Iboy-x/FlyIt-rig-V1/yoke/14-Hubspacing.stl

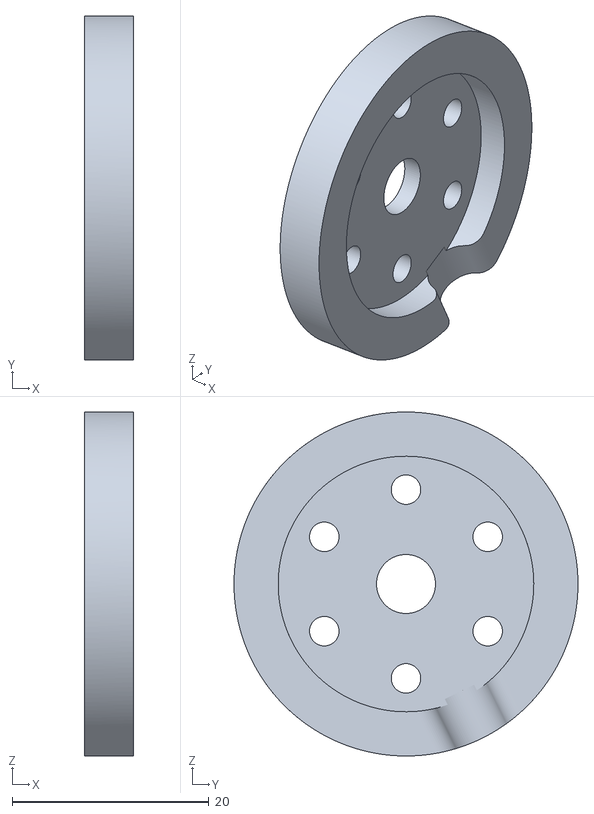
[picture p21: CAD file, 2025-06-05]
yoke/14-Hubspacing.stl
5.00 x 35.0 x 35.0
