Iboy-x/FlyIt-rig-V1/Padel/6-Rod Holder 1.stl

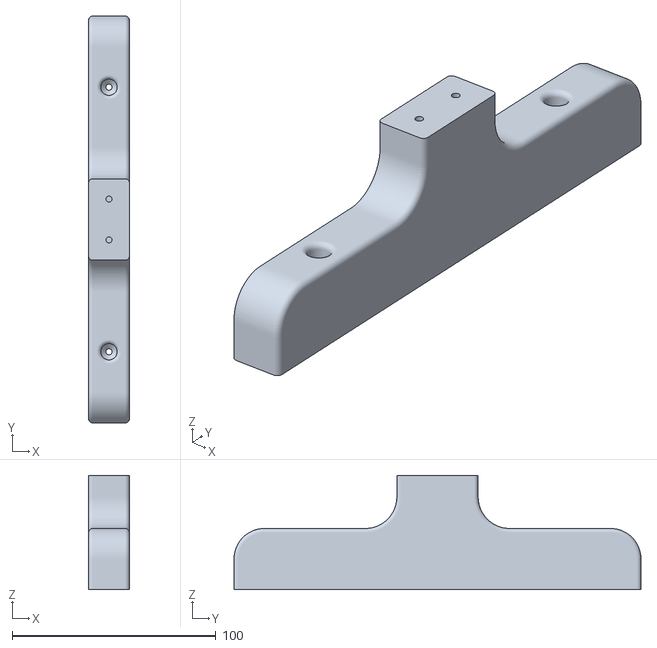
[picture p22: CAD file, 2025-06-15]
Padel/6-Rod Holder 1.stl
20.0 x 200.0 x 56.0
