Iboy-x/FlyIt-rig-V1/yoke/12-LBHupperpart.stl

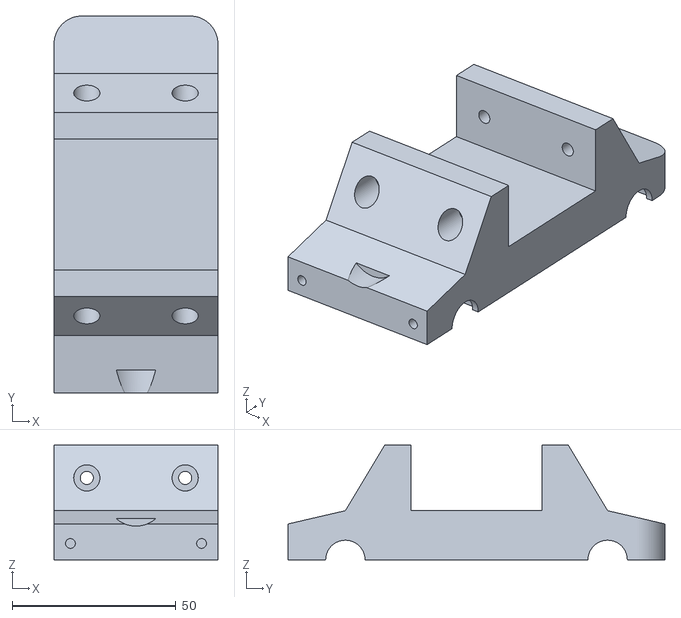
[picture p23: CAD file, 2025-06-05]
yoke/12-LBHupperpart.stl
50.0 x 115.0 x 35.0
