Iboy-x/FlyIt-rig-V1/Padel/1-Padels x2.stl

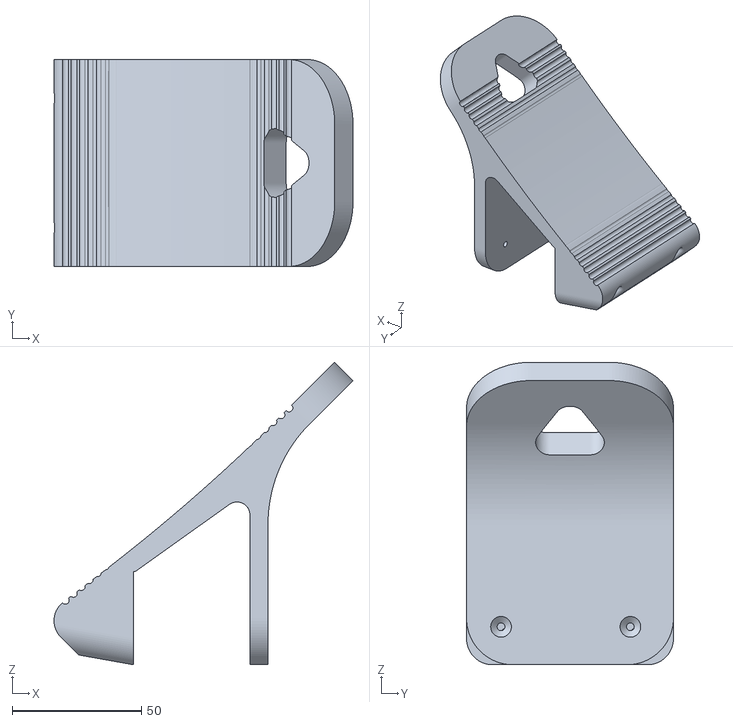
[picture p24: CAD file, 2025-06-15]
Padel/1-Padels x2.stl
115.6 x 80.0 x 116.9
