Iboy-x/FlyIt-rig-V1/Padel/5-Gear-holder.stl

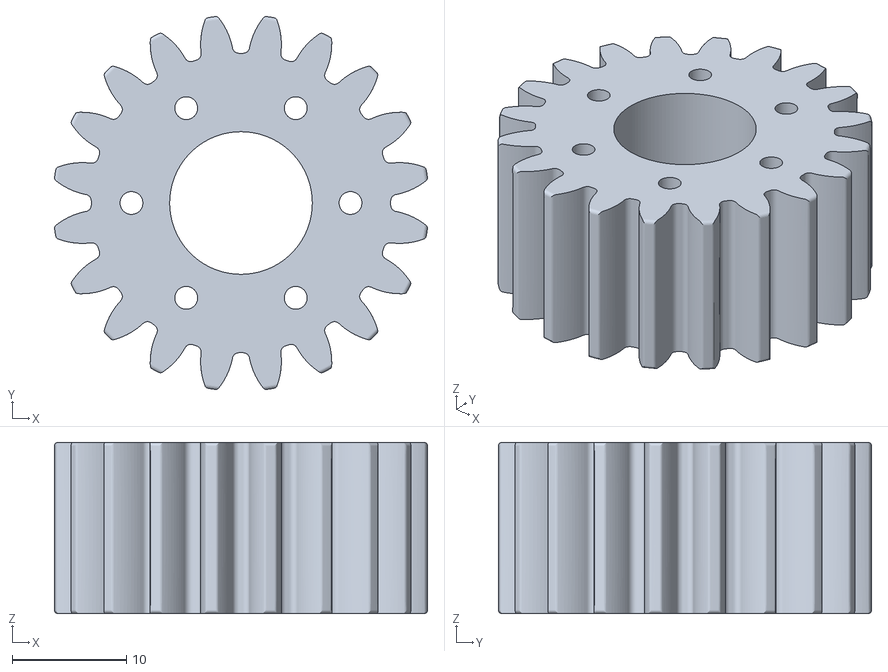
[picture p25: CAD file, 2025-06-15]
Padel/5-Gear-holder.stl
32.7 x 32.7 x 15.0
