Iboy-x/FlyIt-rig-V1/yoke/5-Rodends2.stl

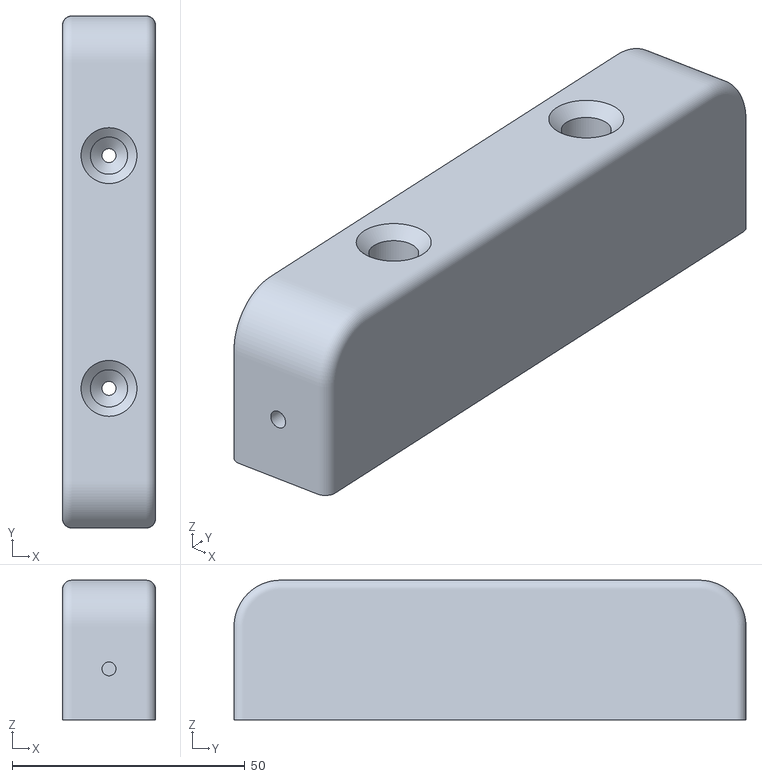
[picture p26: CAD file, 2025-06-05]
yoke/5-Rodends2.stl
20.0 x 110.0 x 30.0
