Iboy-x/FlyIt-rig-V1/Padel/3-BarPadHol.stl

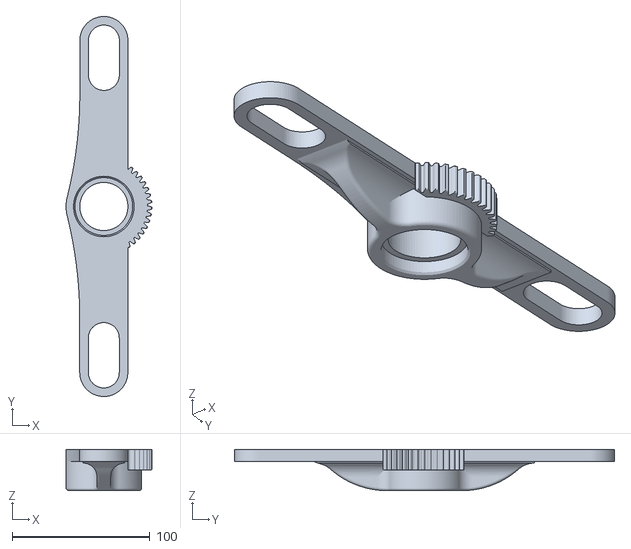
[picture p27: CAD file, 2025-06-15]
Padel/3-BarPadHol.stl
62.5 x 276.3 x 30.0
