Iboy-x/FlyIt-rig-V1/Padel/7- Rod Holder 1.stl

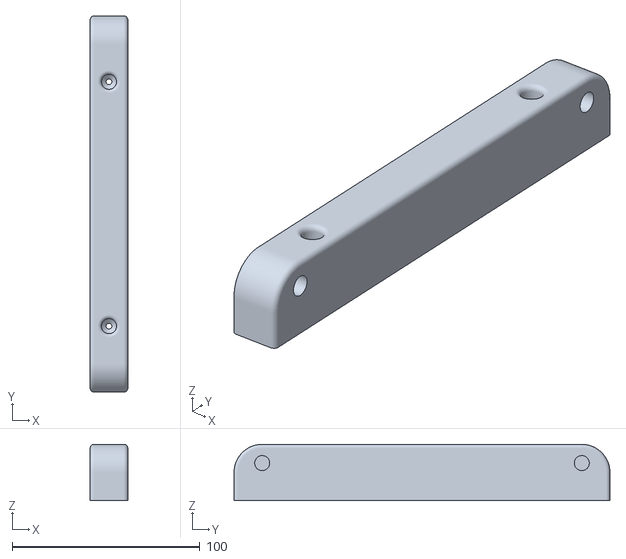
[picture p28: CAD file, 2025-06-15]
Padel/7- Rod Holder 1.stl
20.0 x 200.0 x 30.0
