Iboy-x/FlyIt-rig-V1/yoke/6-RackStrip.stl

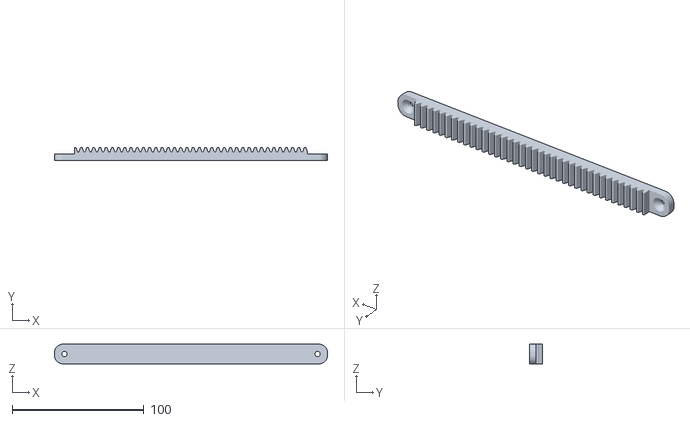
[picture p29: CAD file, 2025-06-05]
yoke/6-RackStrip.stl
207.0 x 10.0 x 15.0
