Iboy-x/FlyIt-rig-V1/Padel/4-pot,BarHolder.stl

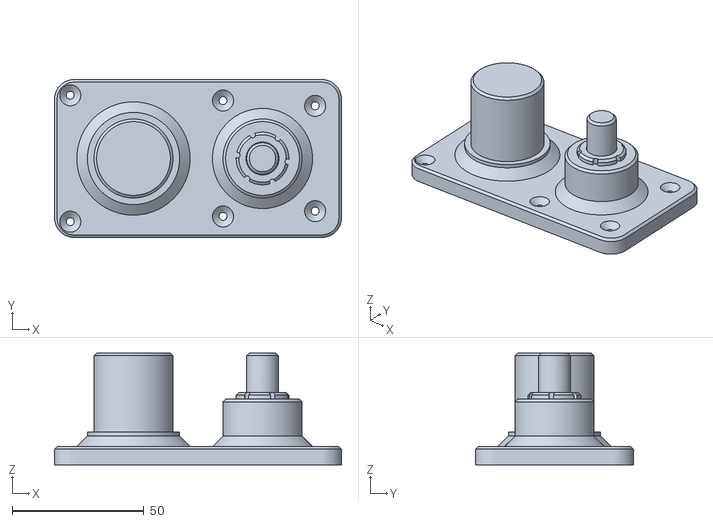
[picture p30: CAD file, 2025-06-15]
Padel/4-pot,BarHolder.stl
109.0 x 60.0 x 42.5
