Iboy-x/FlyIt-rig-V1/yoke/16-bearingcasingdown.stl

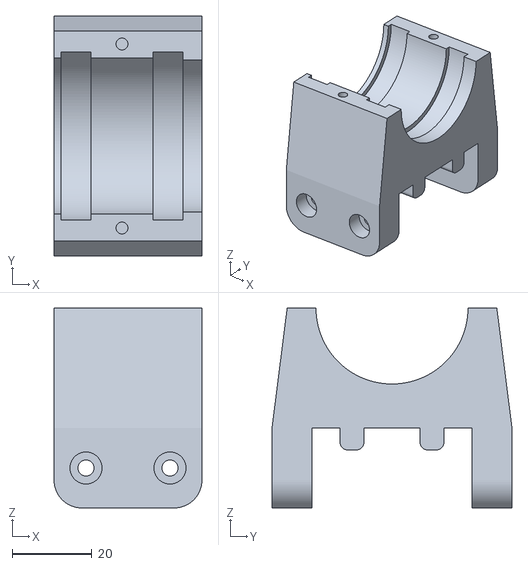
[picture p31: CAD file, 2025-06-05]
yoke/16-bearingcasingdown.stl
37.0 x 60.0 x 50.0
