Iboy-x/FlyIt-rig-V1/yoke/13-LBHlowerpart.stl

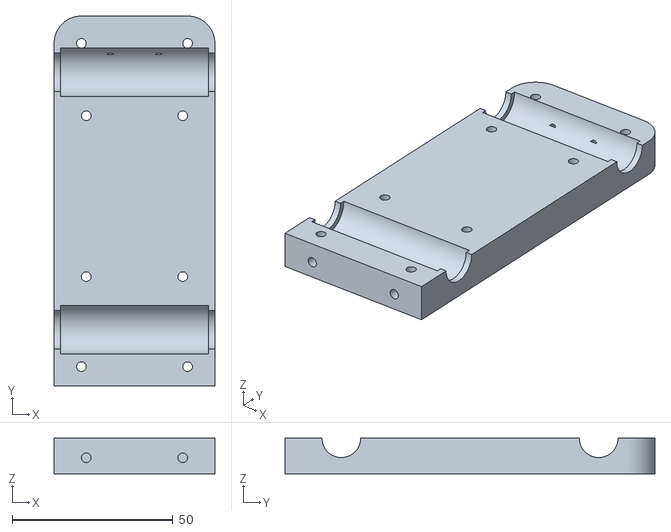
[picture p32: CAD file, 2025-06-05]
yoke/13-LBHlowerpart.stl
50.0 x 115.0 x 11.0
