Iboy-x/FlyIt-rig-V1/yoke/2-Yoke Shaft.stl

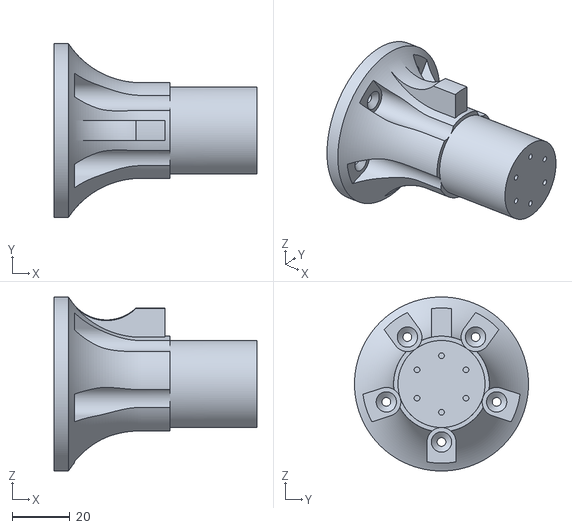
[picture p33: CAD file, 2025-05-29]
yoke/2-Yoke Shaft.stl
70.0 x 60.0 x 60.0
