Iboy-x/FlyIt-rig-V1/yoke/10-PotentiometerRoller.stl

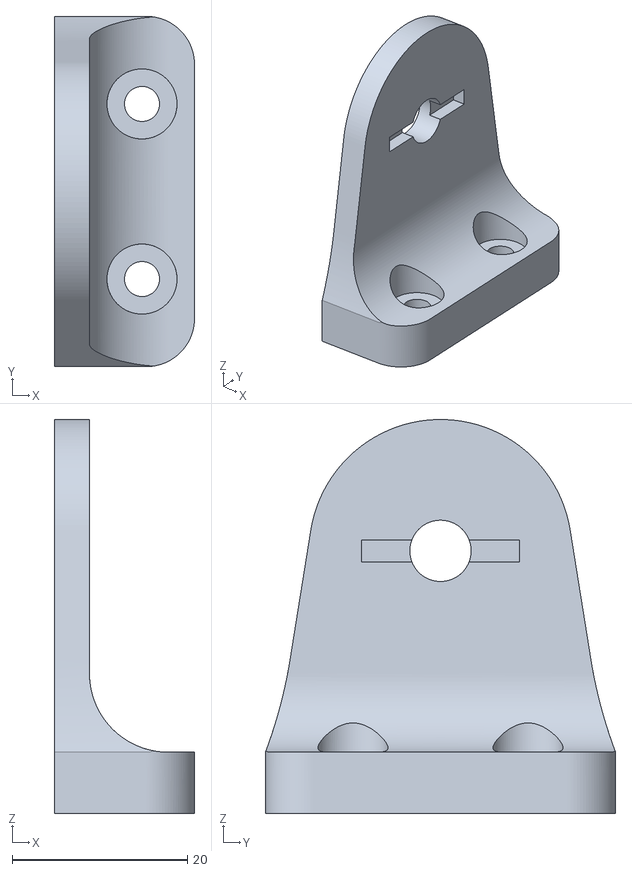
[picture p34: CAD file, 2025-05-29]
yoke/10-PotentiometerRoller.stl
16.0 x 40.0 x 45.0
