Iboy-x/FlyIt-rig-V1/yoke/1-Yoke.stl

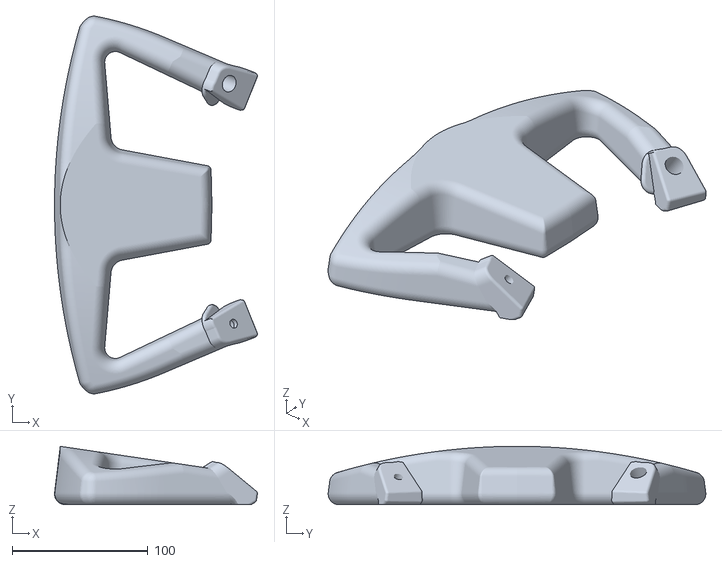
[picture p35: CAD file, 2025-05-21]
yoke/1-Yoke.stl
149.6 x 278.2 x 43.0
